cadaritre/TresVizoRTK/hardware/power-modules/PANEL.md

# Panel exterior

Usar el panel del [receptor V2.2](../../mechanical/v2.2/README.md): pantalla OLED, botón de 12 mm, conector de carga JST-XH de 2 pines y dos LED. No hay panel auxiliar. No se ha ensayado físicamente.

| Elemento | Posición X / Z, mm | Montaje V1 |
| --- | --- | --- |
| USB-C Adafruit 5871 | 0 / 132 | Cuatro apoyos y dos M2×5 diagonales; setback 1.2 mm. |
| Estado RGB | −4 / 121 | Difusor al ras y LED Steren Ø5. |
| Carga | +4 / 121 | Difusor y corredor para guía óptica desde PowerBoost. |
| Botón | 0 / 110 | Actuador cautivo y cartucho con lengüeta más un M3×8. |
| Cierres del panel | 0 / 96 y 0 / 139 | Dos M3×8 de cabeza botón, apoyo plano. |

Panel, actuador y cartucho son tres impresiones estructurales; los dos difusores usan material translúcido. El interior incorpora bandejas para PowerBoost sin USB-A y SparkFun Mk2; ambos con dos bridas y retirada hacia atrás. Tiny-Adapter conserva su FPC original.

Ver [STL vigentes](../../mechanical/v2.2/generated/stl/), [validación de integración](../../docs/INTEGRATION_REVIEW.md), [BOM de tornillería](../../mechanical/v2.2/SCREW-BOM.md), [arnés](WIRING.md) y [compra en México](SOURCING_MX.md). La validación CAD no sustituye el primer ajuste físico del AU-101, enchufe o impresión.
