cadaritre/TresVizoRTK/docs/connectivity/KNOWN_LIMITATIONS.md

# Limitaciones conocidas y riesgos

## Tabla GATT vieja en caché del cliente (resuelta en 0.7.12)

Una Mac que se conectó hace tiempo a un firmware antiguo siguió viendo, con 0.7.11 cargado,
**4 características en vez de 5** (sin la de salud `a04c0006`) y la de RTCM **sin** escritura
sin respuesta. El primer escaneo la nombró con el nombre antiguo del equipo («TresVizo-C81D»):
la Mac usa lo que guardó. Sin emparejamiento el cliente no recibe el aviso de «servicios
cambiados» (la pila solo lo manda a emparejados). **Confirmado del lado del equipo**: la
característica de salud existía (handle 52; respuestas 44, solución 47), así que lo que veía la
Mac era su copia vieja. Un iPhone o Android que se conectó con un firmware viejo podía estar
igual.

**Arreglo (0.7.12, decisión del propietario del 28-09-2026): una dirección por tabla GATT.** El
equipo ya no se anuncia con la dirección pública del chip sino con una **aleatoria estática
derivada de ella y de `kGattTableGeneration`** (`lib/protocol/src/ble_address.h`, probada en
`test/ble_address_test.cpp`). Cada vez que la tabla cambia, la generación sube, el equipo
aparece con otra dirección y todo cliente lee la tabla desde cero. **Comprobado el 28-09-2026**
con la misma Mac de la caché vieja: con 0.7.12 vio las 5 características, `a04c0005` con
escritura sin respuesta (propiedades `0xc`) y la salud a 0.99–1.05 s.

- **El costo**: tras una actualización que cambie la tabla, cada teléfono ve un equipo nuevo.
  Se conecta una vez desde «Cerca»; el que quedó en «Recordados» con la dirección vieja ya no
  aparece y se puede olvidar. Pasa **una vez por cambio de tabla**, no en cada actualización.
- `GET /api/ble` dice `gatt_table_generation`, `address`, `address_type` (`random_static`, o
  `public` si la pila no aceptó la aleatoria: entonces vuelve el riesgo de la tabla vieja) y,
  si la pila rechazó la dirección, `address_error`.
- Descartado, para que no se vuelva a proponer sin motivo: **emparejar** (cada recarga del
  firmware o borrado de la NVS rompe el emparejamiento y obliga a olvidarlo en los ajustes del
  teléfono) y el aviso de «servicios cambiados» sin emparejar (sale bien del equipo, `ESP_OK`,
  pero macOS no redescubre; sigue en el firmware **apagado por defecto** como sonda,
  `-DTRESVIZO_BLE_SERVICE_CHANGED`).
- Las apps siguen degradando bien si una característica falta (la salud no se exige para estar
  lista; el modo de escritura del RTCM sale de las propiedades descubiertas; iOS atiende
  `didModifyServices`) y enseñan «Tabla Bluetooth desactualizada» en Equipo › Bluetooth si con
  protocolo 3 no ven la salud. Android **no** llama a `BluetoothGatt.refresh()` (lo decía una
  versión anterior de este documento; no estaba en el código).

## Seguridad (BLE abierto por decisión del propietario desde 0.6.2; F07 cerrado en 0.7.13)

- **Cualquiera al alcance puede conectarse** y escribir órdenes y correcciones: no hay
  emparejamiento, PIN ni cifrado. Las órdenes incluyen `POST /api/restart` y cambiar de modo.
- Mitigaciones vigentes: un solo cliente a la vez (el equipo deja de anunciarse mientras hay
  uno conectado); el transporte se apaga desde Conexiones y se persiste; el RTCM por BLE se
  ignora en modo base; la carga de firmware y la lectura de grabaciones no van por BLE.
- **Hasta 0.7.12 la contraseña del Wi-Fi propio sí salía por BLE** (`ap_password` en
  `GET /api/config`, `GET /api/wifi/networks` y las respuestas de guardado). Este documento
  decía lo contrario: el filtro solo cortaba `/api/access`. Con ella se llegaba al HTTP, que no
  pide clave, y desde ahí a cargar un firmware **sin firma** (hallazgo F07).
- **Desde 0.7.13**, dos medidas:
  - Ninguna respuesta BLE lleva credenciales: `protocol::stripSecrets`
    (`lib/protocol/src/secret_redaction.h`, prueba `test/secret_redaction_test.cpp`) quita a
    cualquier profundidad toda clave con nombre de credencial que no sea booleana. HTTP, USB y
    WebSocket no cambian: el panel la sigue leyendo y reenviando. Una app que lea la
    configuración por BLE ya no la recibe (en el código de iOS: «—» y «Copiar» desactivado).
  - La OTA exige la firma ECDSA P-256 del propietario, y `rollback` solo vuelve a imágenes que
    también la exijan (`firmware/esp32/README.md`, «Actualización por OTA»).
- **Lo que sigue abierto, a sabiendas:** cambiar la contraseña del AP o añadir una red Wi-Fi
  **sí** se admite por BLE (comodidad, decisión del propietario). Alguien cerca puede fijar una
  contraseña que conoce, o unir el equipo a una red suya, y entrar al HTTP: leer y cambiar la
  configuración, reiniciar, cambiar de modo, o dejar al propietario fuera del Wi-Fi hasta que
  la cambie de nuevo por la app o el USB. Lo que ya no puede es instalar un firmware ajeno.
- Riesgo real en obra: alguien cerca con una app genérica puede reiniciar el equipo o mandarle
  correcciones basura (el CRC las filtra si están mal formadas, no si son de otra base).
- Endurecimiento posible sin fricción: exigir que la primera orden de una conexión venga de una
  app que se identifique (no es seguridad fuerte), o volver al emparejamiento «Just Works» con
  cifrado para cortar la escucha pasiva. Lo decide el propietario.

## Rendimiento y memoria

- **RTCM con respuesta** (clientes con tabla vieja o firmware ≤ 0.7.10) topa en ≈2.8 kB/s a
  30 ms de intervalo. Un caster MSM7 de cuatro constelaciones no cabe; MSM4 va justo.
- **UART al UM980 a 115200** (≈11.5 kB/s) compartida por RTCM y órdenes. Suficiente para RTCM a
  1 Hz; subir la velocidad exige verificar la configuración del puerto del UM980 y el cableado
  (AGENTS.md: manuales antes que suposiciones).
- La biblioteca BLE de Arduino arma un volcado hexadecimal con `malloc`/`free` **en cada
  escritura** aunque los registros estén apagados (`BLECharacteristic.cpp`, `buildHexData`), y
  copia cada valor a un `std::string`. Con RTCM sin respuesta son decenas de reservas por
  segundo: vigilar `min_free_heap_bytes` en sesiones largas.
- 0.7.11 bajó el heap interno libre de ~106 KB a ~97 KB tras arrancar (cola estática de 8 KiB).
  Hay 2 MB de PSRAM libres: la cola puede ir ahí si hace falta.

## Menores, vistos al escribir el decodificador del banco

- `Rtcm3Parser::overflow` (`lib/gnss/src/rtcm3.h:25`) no sube nunca: el contador existe pero
  siempre vale 0.
- Una petición BLE con JSON inválido recibe `400 invalid_request` **sin `id`**: el cliente no la
  puede asociar a su orden y la da por vencida al agotar el plazo. Solo pasa con una trama
  corrupta; las apps no mandan JSON inválido.

## Sin validar todavía

RTCM **sin** respuesta de punta a punta (ningún cliente de hoy tenía la tabla al día), sesión
larga, coexistencia Wi-Fi/BLE con NTRIP del equipo activo, Android, segundo plano en iOS,
reconexiones reales fuera de alcance, y todo lo que necesita fix (bajo techo no hubo).
