cadaritre/TresVizoRTK/firmware/esp32/include/gnss_control.h

#pragma once
#include <Arduino.h>
#include <ArduinoJson.h>
namespace gnss_control {
void begin();
// Consume un bloque completo con una sola toma del mutex. Antes se tomaba y
// soltaba el semaforo una vez por byte desde la tarea UART.
void feed(const char* data, size_t length);
void tick(HardwareSerial& uart);
bool busy();
// Cancela solo ese trabajo (0: el vigente), sin cortar un comando UART a medias.
void cancel(uint32_t expectedJob = 0);
bool baseRequested();
bool roverReady();
// El receptor trabaja como base. Un equipo base no consume correcciones: las
// produce. Sin esta distincion el panel puede decir a la vez que es base y
// que esta recibiendo correcciones, que no tiene sentido.
bool isBase();
// El modo leido, sin ventana de caducidad. roverReady() caduca a los 30 s
// porque sirve para autorizar una conexion, no para informar del papel.
bool isRover();
const char* heightReference();
// Mascara de elevacion del receptor segun la ultima lectura o aplicacion (5 por
// defecto del manual N4). La usa el conteo de satelites visibles.
double elevationMaskDeg();
// El ultimo trabajo que cambio la configuracion termino con un SAVECONFIG que
// el receptor confirmo con OK. Es lo que publican `saved` y
// `persisted_to_receiver`. Falso desde que empieza cualquier trabajo que
// escriba en el receptor hasta ese OK.
bool persisted();
int start(JsonVariantConst body, JsonDocument& out);
// Coordenada conocida o promedio del receptor. Envia `CONFIG UNDULATION
// 0.0000`, `MODE BASE ...`, `MODE` y, solo si el modo leido es base,
// `SAVECONFIG`.
int applyBase(JsonVariantConst plan, JsonDocument& out);
void status(JsonObject out);
// Ultima configuracion avanzada aplicada y leida del receptor. Refleja lo que
// este firmware envio o leyo, no una lectura continua del UM980.
void profile(JsonObject out);
}
