cadaritre/TresVizoRTK/firmware/esp32/src/base_survey.cpp

#include "base_survey.h"
#include "base_average.h"
#include "base_plan.h"
#include "gnss_receiver.h"
#include "gnss_control.h"
#include "ntrip_input.h"
#include "correction_router.h"
#include "config_rules.h"
#include <Arduino.h>
#include <atomic>
#include <cmath>

namespace base_survey {
namespace {
using base_average::Quality;

std::atomic<const char*> state{"idle"};
std::atomic<const char*> reason{""};
Quality required = Quality::Fixed;
uint32_t wantedSeconds = 60;
uint32_t startedAt = 0;
uint32_t samples = 0;
uint32_t stationId = 0;
double antennaVertical = 0;
// Hay una altura de antena del operador que enseñar: sin promedio pedido en
// esta sesión no la hay, y se publica nula en vez de cero.
bool antennaKnown = false;
// Sumas en doble precisión. A un metro de escala y unas miles de épocas no hay
// pérdida apreciable, y evita el coste de un acumulador compensado.
double sumLat = 0, sumLon = 0, sumHeight = 0;
// Llegada de la última época aceptada, en el reloj monotónico del ESP32. Es el
// instante de llegada, no el de medición: lo que se comprueba al cerrar es si
// el receptor seguía entregando, y eso lo dice el reloj de quien recibe.
uint64_t lastSampleArrivalUs = 0;
// El motivo del fallo vive fuera del atomic: este guarda el puntero y necesita
// que la cadena siga existiendo.
String failureText;
uint32_t lastEpoch = UINT32_MAX;
uint32_t applyingJob = 0;

const char* qualityName(Quality value) {
    switch (value) {
        case Quality::Fixed: return "rtk_fixed";
        case Quality::Float: return "rtk_float";
        case Quality::Single: return "standalone";
        default: return "any";
    }
}
void stop(const char* nextState, const char* why) {
    state = nextState;
    reason = why;
}

// Tiempo cumplido y época ya vista: declarar la media o cancelar.
void close(uint32_t now, uint64_t nowUs) {
    const uint32_t lastSampleAgeMs = samples ? uint32_t((nowUs - lastSampleArrivalUs) / 1000) : UINT32_MAX;
    switch (base_average::closeVerdict(now - startedAt, wantedSeconds, samples, lastSampleAgeMs)) {
        case base_average::Close::Wait:
            return;
        case base_average::Close::StaleLastSample:
            stop("cancelled", "La última época válida quedó vieja antes de terminar: el receptor dejó de dar la solución exigida al final del promedio. La coordenada no describiría los últimos segundos.");
            return;
        case base_average::Close::TooFewSamples:
            stop("cancelled", "Muy pocas épocas válidas para el tiempo pedido: el receptor entregó la solución a saltos. La coordenada no sería un promedio de ese tiempo.");
            return;
        case base_average::Close::Apply:
            break;
    }
    // Tiempo cumplido: aplicar la media como coordenada de la base.
    const auto heights = base_plan::surveyHeights(sumHeight / samples, antennaVertical);
    JsonDocument plan;
    plan["method"] = "known";
    plan["station_id"] = stationId;
    plan["latitude_deg"] = sumLat / samples;
    plan["longitude_deg"] = sumLon / samples;
    // La media es la posición de la antena y se declara tal cual; ver
    // `base_plan::surveyHeights`. La altura de antena no se suma aquí.
    plan["arp_ellipsoid_height_m"] = heights.declaredEllipsoidHeightM;
    // Una base no consume correcciones, y tenerlas activas bloquea la
    // aplicación del modo. Se cierran aquí en vez de fallar al final de
    // un promedio de varios minutos por algo que sabíamos de antemano.
    JsonDocument out;
    const int code = gnss_control::applyBase(plan.as<JsonVariantConst>(), out);
    if (code == 202) {
        applyingJob=out["job_id"];
        ntrip_input::releaseForBase();
        correction_router::select("none");
        // Lanzado no es aplicado: el receptor todavía no ha contestado.
        // Decir "applied" aquí era la misma mentira de siempre.
        stop("applying", "Enviando la coordenada al receptor…");
    } else {
        // El motivo real, no uno inventado: antes decía que lo rechazaba
        // el receptor cuando el receptor no había llegado a verlo.
        failureText = out["message"].is<const char*>()
            ? String(out["message"].as<const char*>())
            : String("No se pudo aplicar la coordenada promediada.");
        stop("failed", failureText.c_str());
    }
}
}

void begin() { state = "idle"; }

bool active() { return !strcmp(state.load(), "averaging"); }
void cancel(const char* why) {
    if(!strcmp(state.load(),"applying"))gnss_control::cancel(applyingJob);
    if(active() || !strcmp(state.load(),"applying"))stop("cancelled",why);
}

void tick() {
    // Esperando la confirmación del receptor tras enviar la coordenada.
    if (!strcmp(state.load(), "applying")) {
        JsonDocument control;gnss_control::status(control.to<JsonObject>());
        if(control["job_id"].as<uint32_t>()!=applyingJob) {
            stop("cancelled","Sustituido por otra operación del GPS.");return;
        }
        if (gnss_control::busy()) return;
        if (!gnss_control::isBase()) {
            stop("failed", "El receptor no confirmó el modo base. Consulta su estado en GPS avanzado.");
        } else if (!gnss_control::persisted()) {
            // Es base, pero lo aplicado vive solo en la RAM del receptor: un
            // corte lo devuelve a su modo anterior. Se dice, no se calla.
            stop("applied", "La base quedó aplicada, pero el receptor no confirmó el guardado (SAVECONFIG): si se apaga, volverá a su modo anterior. Revisa el estado en GPS avanzado.");
        } else {
            stop("applied", "");
        }
        return;
    }
    if (!active()) return;
    const auto snapshot = gnss_receiver::snapshot();
    const auto& s = snapshot.solution;
    const uint32_t now = millis();
    const uint64_t nowUs = esp_timer_get_time();

    // Sin épocas frescas no se promedia y, pasados unos segundos, se cancela:
    // seguir contando el tiempo sin datos daría un promedio de nada.
    if (!snapshot.enabled || !snapshot.accepted || nowUs - s.arrival_us > base_average::kEpochStaleUs) {
        if (now - startedAt > base_average::kSilenceGraceMs) {
            stop("cancelled", "El receptor dejó de entregar posiciones durante el promedio.");
        }
        return;
    }
    if (s.utc_ms == lastEpoch) {
        close(now, nowUs);
        return;
    }
    lastEpoch = s.utc_ms;
    switch (base_average::classify(required, s.quality, s.has_position,
                                   s.latitude_deg, s.longitude_deg, s.altitude_msl_m)) {
        case base_average::Epoch::NoPosition:
            // Antes esta época se saltaba y el promedio seguía: al cumplirse el
            // tiempo se declaraba la base con las muestras de antes del corte.
            stop("cancelled", "El receptor entregó una época sin posición o sin altura: se perdió la solución durante el promedio. La coordenada habría quedado con muestras de antes del corte.");
            return;
        case base_average::Epoch::LostQuality:
            // Esto es lo que pidió el propietario: si la calidad exigida se pierde a
            // mitad del promedio, se cancela y se dice por qué, en vez de terminar
            // con una media contaminada que nadie sabría que lo está.
            stop("cancelled", "Se perdió la calidad de solución exigida durante el promedio. La coordenada habría quedado contaminada.");
            return;
        case base_average::Epoch::Accept:
            break;
    }
    sumLat += s.latitude_deg;
    sumLon += s.longitude_deg;
    // GGA entrega altura sobre el geoide; la base se declara en elipsoidal.
    sumHeight += base_plan::ggaEllipsoidHeightM(s.altitude_msl_m, s.geoid_separation_m);
    lastSampleArrivalUs = s.arrival_us;
    ++samples;
}

void status(JsonObject out) {
    out["state"] = state.load();
    out["reason"] = reason.load();
    out["required_quality"] = qualityName(required);
    out["seconds_requested"] = wantedSeconds;
    out["samples"] = samples;
    const uint32_t elapsed = active() ? (millis() - startedAt) / 1000 : 0;
    out["seconds_elapsed"] = elapsed;
    out["case_offset_m"] = base_plan::kCaseOffsetM;
    // La altura de antena que dio el operador, para que el desglose de la cota
    // de la marca se pueda enseñar entero. Nula si no se ha pedido promedio.
    if (antennaKnown) out["antenna_vertical_m"] = antennaVertical;
    else out["antenna_vertical_m"] = nullptr;
    // Media acumulada hasta ahora: el usuario ve la coordenada que va a quedar
    // mientras se forma, en vez de esperar a ciegas a que termine.
    if (samples) {
        const auto heights = base_plan::surveyHeights(sumHeight / samples, antennaVertical);
        out["latitude_deg"] = sumLat / samples;
        out["longitude_deg"] = sumLon / samples;
        // Lo que se declara en MODE BASE: la media de la antena, tal cual.
        // Hasta 0.7.12 llevaba sumadas la antena y el case (ver base_plan.h).
        out["height_to_set_m"] = heights.declaredEllipsoidHeightM;
        // Cota elipsoidal de la marca en el suelo: media − antena − case.
        // Informativa; no se envía al receptor.
        out["mark_ellipsoid_height_m"] = heights.markEllipsoidHeightM;
    } else {
        out["latitude_deg"] = nullptr;
        out["longitude_deg"] = nullptr;
        out["height_to_set_m"] = nullptr;
        out["mark_ellipsoid_height_m"] = nullptr;
    }
    // Sin ondulación informada la altura elipsoidal sería la del geoide: se
    // advierte en vez de entregar una coordenada con decenas de metros de error.
    const auto snapshot = gnss_receiver::snapshot();
    out["geoid_separation_known"] = std::isfinite(snapshot.solution.geoid_separation_m);
}

int request(const String& method, JsonVariantConst body, JsonDocument& out) {
    if (method == "GET") { status(out.to<JsonObject>()); return 200; }
    if (method != "POST" || !body.is<JsonObjectConst>()) return 400;
    const String action = body["action"] | "";
    if (action == "cancel") {
        cancel("Cancelado desde el panel; los comandos ya transmitidos pueden haber cambiado el receptor.");
        stop("cancelled", "Cancelado desde el panel; los comandos pendientes no se enviarán.");
        status(out.to<JsonObject>());
        return 200;
    }
    if (action != "start") return 400;
    // Dos segundos son 10 épocas a 5 Hz: con solución fija es un promedio
    // legítimo, y exigir más era una regla inventada. El mínimo de épocas que
    // se exige al cerrar lo fija `base_average::minSamples`.
    if (!body["seconds"].is<unsigned>() || body["seconds"].as<unsigned>() < 2 ||
        body["seconds"].as<unsigned>() > 900) {
        out["message"] = "El tiempo de promedio va de 2 a 900 segundos."; return 400;
    }
    if (!body["station_id"].is<unsigned>() || body["station_id"].as<unsigned>() > 4095) {
        out["message"] = "Identificador de estación: 0 a 4095."; return 400;
    }
    if (!body["antenna_vertical_m"].is<double>() ||
        body["antenna_vertical_m"].as<double>() < 0 || body["antenna_vertical_m"].as<double>() > 100) {
        out["message"] = "Altura de antena: 0 a 100 m."; return 400;
    }
    Quality requestedQuality=Quality::Fixed;
    const String quality = body["quality"] | "rtk_fixed";
    if (quality == "rtk_fixed") requestedQuality = Quality::Fixed;
    else if (quality == "rtk_float") requestedQuality = Quality::Float;
    else if (quality == "standalone") requestedQuality = Quality::Single;
    else if (quality == "any") requestedQuality = Quality::Any;
    else { out["message"] = "Calidad admitida: rtk_fixed, rtk_float, standalone o any."; return 400; }

    const auto snapshot = gnss_receiver::snapshot();
    if (!base_average::matches(requestedQuality, snapshot.solution.quality)) {
        out["message"] = "La solución actual no cumple la calidad exigida. Espera a alcanzarla o elige otra.";
        return 409;
    }
    gnss_control::cancel();
    required=requestedQuality;
    wantedSeconds = body["seconds"];
    stationId = body["station_id"];
    antennaVertical = body["antenna_vertical_m"];
    antennaKnown = true;
    sumLat = sumLon = sumHeight = 0;
    samples = 0;
    lastSampleArrivalUs = 0;
    lastEpoch = UINT32_MAX;
    startedAt = millis();
    stop("averaging", "");
    status(out.to<JsonObject>());
    return 202;
}
}
