cadaritre/TresVizoRTK/firmware/esp32/include/ntrip_input.h

#pragma once
#include <ArduinoJson.h>
namespace ntrip_input {
void begin();
// Llamar bajo el mismo mutex del instrumento que request/profileRequest.
void tick();
void stopForUser();
bool active();
int request(const String& method,JsonVariantConst body,JsonDocument& out);
// Perfiles guardados en NVS y autoconexión al último elegido. "Ninguno" también
// se guarda: es una decisión del usuario, no la ausencia de una.
int profileRequest(const String& method,JsonVariantConst body,JsonDocument& out);
// Lista de puntos de montaje publicada por el caster. Comparte radio con el
// flujo, así que solo se resuelve con la conexión detenida.
int sourcetableRequest(const String& method,JsonVariantConst body,JsonDocument& out);
// Suelta la conexion porque el equipo va a trabajar como base. No es lo mismo
// que detenerla el usuario: al volver a rover, esta se reanuda sola y la del
// usuario no, porque respetar una decision suya es distinto de deshacer un
// apano nuestro.
void releaseForBase();
void status(JsonObject out);
}
